Kalilinuxloverr/Desk-Mate/docs/logo/README.md

# Logo

- `deskmate.svg` — quadratische Bildmarke: ein eigenständiger, freundlicher Zukunfts-Roboter mit hellem Gehäuse, dunklem Visier und türkisfarbenen Augen.
- `deskmate-wordmark.svg` — horizontale Wortmarke mit 1:1 übernommener Bildmarke, Trennlinie und Systemschrift. Das Icon wird nicht gestreckt.

Farben sind zugleich die Ampelfarben im UI: Grün #3DDC84 (frei), Gelb #FFC857 (arbeitet), Rot #FF5C5C (braucht dich).
